MUNAKATA-EPC/Hercules_2022/KiCad_Project/2021/電源基板回路(2).pdf

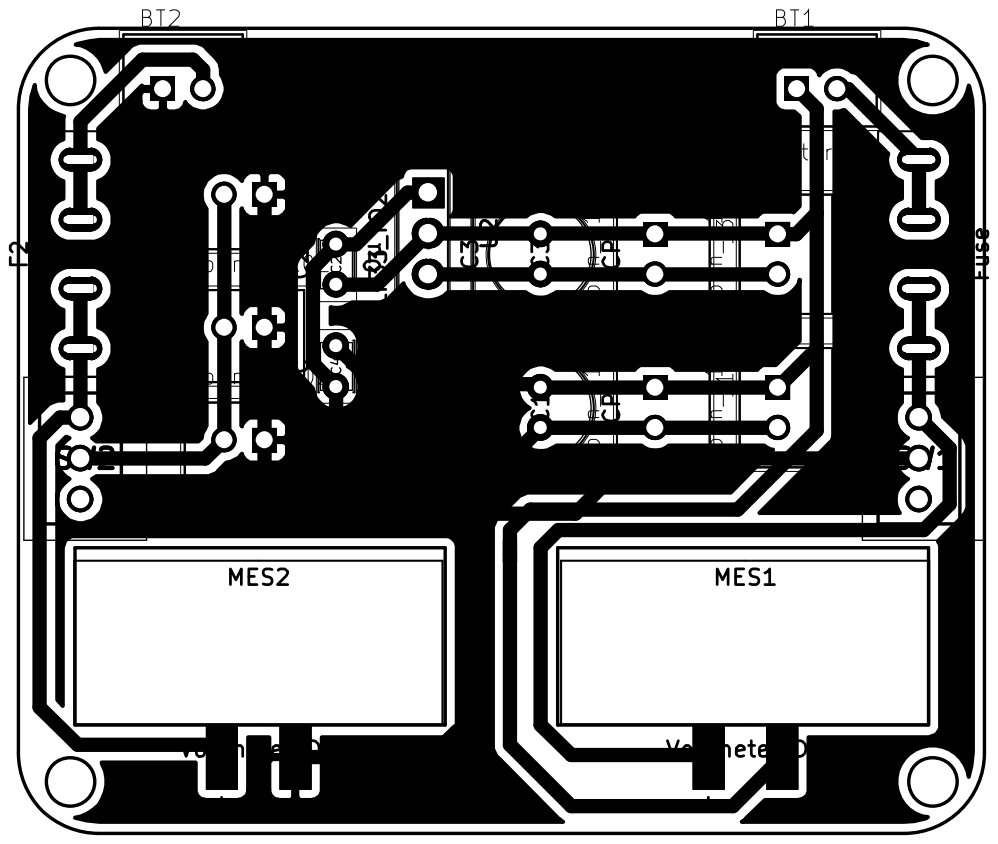
[picture p28: page 1]
