MUNAKATA-EPC/Hercules_2022/KEIHANNA_MAIN-teensy40/include/pid.h

void pid() {
  deviation = IMU_center - IMU;  //偏差:現在角度と目標角度のズレ

  val_I += deviation;  //偏差の積分値

  if (val_I < -30000) {
    val_I = -30000;
  } else if (val_I > 30000) {
    val_I = 30000;
  }

  if (abs(deviation) <= 2) {
    val_I = 0;
  }

  val_D = deviation - old_deviation;  //偏差の微分値
  old_deviation = deviation;  //微分用前回偏差値の保存

  operation_A = gain_P * deviation;  //比例ゲイン*偏差
  operation_B = gain_I * val_I;  //積分ゲイン*偏差の積分値
  operation_C = gain_D * val_D;  //微分ゲイン*偏差の微分値

  operation_A = operation_A + operation_B + operation_C;  //最終的な操作量

  if (operation_A < -set_limit_operation) {
    operation_A = -set_limit_operation;  //下限値
  } else if (operation_A > set_limit_operation) {
    operation_A = set_limit_operation; //上限値
  }
}
