MUNAKATA-EPC/Hercules_2022/KEIHANNA_MAIN-teensy40/include/control_LED.h

void control_LED() {
  if (digitalRead(LINE_1) == LOW || digitalRead(LINE_2) == LOW || digitalRead(LINE_3) == LOW || digitalRead(LINE_4) == LOW) {
    digitalWrite(LED, HIGH);
  } else {
    digitalWrite(LED, LOW);
  }
}
