MUNAKATA-EPC/Hercules_2022/OpenMV プログラム/FUKUDA ver 6.py

#Single Color RGB565 Blob Tracking Example
#  福田ロボットの調整用
# This example shows off single color RGB565 tracking using the OpenMV Cam.

import sensor, image, time, math#ライブラリーの読み込み
from pyb import UART, LED, Pin, Timer, DAC#ライブラリーの読み込み

red_led   = LED(1)                  #下２１行目までLEDのセットアップ
green_led = LED(2)
blue_led  = LED(3)
ir_led    = LED(4)

def led_control(x):
 if   (x&1)==0: red_led.off()
 elif (x&1)==1: red_led.on()
 if   (x&2)==0: green_led.off()
 elif (x&2)==2: green_led.on()
 if   (x&4)==0: blue_led.off()
 elif (x&4)==4: blue_led.on()
 if   (x&8)==0: ir_led.off()
 elif (x&8)==8: ir_led.on()

threshold_index = 0 # 0 for red, 1 for green, 2 for blue

# Color Tracking Thresholds (L Min, L Max, A Min, A Max, B Min, B Max)
# The below thresholds track in general red/green/blue things. You may wish to tune them...
thresholds1 = [(8, 100, 39, 82, -26, 71)]#メイン
#thresholds1 = [(0, 100, 53, 63, 31, 39)]
#thresholds1 = [(45, 90, 13, 84, -1, 64)]#検証１
#thresholds1 = [(53, 88, 48, 85, -22, 40)]#検証2
thresholds3 = [(0, 0, 40, 73, 26, 57)]#ゴール（青色）
thresholds2 = [(0, 100, 11, 31, -67, -45)]#ゴール（青色）
#thresholds2 = [(0, 100, -12, 17, 45, 72)]#ゴール（黄色）
#上で色の変更可　ただLAB色空間での探知である
# generic_blue_thresholds
uart = UART(3, 115200, timeout_char=1000)

sensor.reset()
sensor.set_pixformat(sensor.RGB565)#カラースケール
sensor.set_framesize(sensor.QVGA)#解像度
sensor.skip_frames(time = 400)#描写速度
sensor.set_contrast(1)#コントラスト
sensor.set_brightness(-2)#明るさ
sensor.set_saturation(1)#彩
sensor.set_auto_gain(False) # must be turned off for color tracking
sensor.set_auto_whitebal(False,(-5.82073, -5.019987, 0.5176831))# must be turned off for color tracking
clock = time.clock()

tim1 = Timer(4, freq=1000)
#tim2 = Timer(8, freq=1000)

dac = DAC(Pin("P6"),bits=12)

# Only blobs that with more pixels than "pixel_threshold" and more area than "area_threshold" are
# returned by "find_blobs" below. Change "pixels_threshold" and "area_threshold" if you change the
# camera resolution. "merge=True" merges all overlapping blobs in the image.

while(True):  #メインループ
 n=0#ボールカラーを取ったブロックの個数（for文の繰り返した回数）
 N=0#ゴールの色を取ったブロックの個数（for文の繰り返した回数）
 m=0
 cut_fro_and_bak=130#画面上での横線の定義
 cut_lef_and_rig=160#画面上での縦線の定義
 count=0#ブロックの個数（今話使っていない
 areapf=0
 iwashi=0#取得したブロックの密度の最大値を保存
 haraga=0#取得したブロックの面積の最大値を保存
 shinya=0
 #akiya=[0,0,0,0,0,0,0,0,0,0,0,0,0,0,0,0,0,0,0,0]
 areaA=[0,0,0,0,0,0,0,0,0,0,0,0,0,0,0,0,0,0,0,0]#取得したブロックの面積を配列にして1つの関数に保存
 areaB=[0,0,0,0,0,0,0,0,0,0,0,0,0,0,0,0,0,0,0,0]#取得したブロックの面積を配列にして1つの関数に保存
 areaC=[0,0,0,0,0,0,0,0,0,0,0,0,0,0,0,0,0,0,0,0]
 rectA=[0,0,0,0,0,0,0,0,0,0,0,0,0,0,0,0,0,0,0,0]#取得したブロック（ボール）の中心のX座標、Y座標、ブロックの横幅、縦幅の値を配列にして1つの関数に保存
 rectB=[0,0,0,0,0,0,0,0,0,0,0,0,0,0,0,0,0,0,0,0]#取得したブロック（ゴール）の中心のX座標、Y座標、ブロックの横幅、縦幅の値を配列にして1つの関数に保存
 rectC=[0,0,0,0,0,0,0,0,0,0,0,0,0,0,0,0,0,0,0,0]
 cxA=[0,0,0,0,0,0,0,0,0,0,0,0,0,0,0,0,0,0,0,0]#取得したブロック（ボール）の中心のX座標のみを配列にして1つの関数に保存
 cxB=[0,0,0,0,0,0,0,0,0,0,0,0,0,0,0,0,0,0,0,0]#取得したブロック（ゴール）の中心のX座標のみを配列にして1つの関数に保存
 cxC=[0,0,0,0,0,0,0,0,0,0,0,0,0,0,0,0,0,0,0,0]
 cyA=[0,0,0,0,0,0,0,0,0,0,0,0,0,0,0,0,0,0,0,0]#取得したブロック（ボール）の中心のY座標のみを配列にして1つの関数に保存
 cyB=[0,0,0,0,0,0,0,0,0,0,0,0,0,0,0,0,0,0,0,0]#取得したブロック（ゴール）の中心のY座標のみを配列にして1つの関数に保存
 cyC=[0,0,0,0,0,0,0,0,0,0,0,0,0,0,0,0,0,0,0,0]
 val=[0,0,0,0,0,0,0,0,0,0,0,0,0,0,0,0,0,0,0,0]#画面中心のX座標
 vall=[0,0,0,0,0,0,0,0,0,0,0,0,0,0,0,0,0,0,0,0]#画面中心のY座標
 r=[0,0,0,0,0,0,0,0,0,0,0,0,0,0,0,0,0,0,0,0]#atan2を使って出した角度（単位ラジアン）
 rads=[0,0,0,0,0,0,0,0,0,0,0,0,0,0,0,0,0,0,0,0]#ｒによって出た角度を絶対値に
 riole=[0,0,0,0,0,0,0,0,0,0,0,0,0,0,0,0,0,0,0,0]#ボールの左右有無の判別用
 distanceA=[0,0,0,0,0,0,0,0,0,0,]
 distanceB=[0,0,0,0,0,0,0,0,0,0,]#付け加え三平方
 densityA=[0,0,0,0,0,0,0,0,0,0,0,0,0,0,0,0,0,0,0,0]#ボールの色の取った面積に対する密度
 densityB=[0,0,0,0,0,0,0,0,0,0,0,0,0,0,0,0,0,0,0,0]#ゴールの色の取った面積に対する密度
 clock.tick()
 img = sensor.snapshot()
 for blob in img.find_blobs([thresholds1[threshold_index]], pixels_threshold=1, area_threshold=1, merge=True,margin=25):#下９０行目までカラーボールトラッキング
     n+=1
     cxA[n]=blob.cy()
     cyA[n]=blob.cx()
     rectA[n]=blob.rect()
     val[n]=blob.cy()-cut_fro_and_bak#値の調整　画面中央を座標(0,0)に
     vall[n]=blob.cx()-cut_lef_and_rig
     r[n]=int(math.atan2(-vall[n],-val[n])*100*0.31)#範囲の調整片側１８０度
     #distanceA[n]=int((math.sqrt((math.pow(val[n],2))+(math.pow(vall[n],2))))*29.16666666666667)#２点間の距離の公式
     distanceA[n]=int((math.sqrt((math.pow(val[n],2))+(math.pow(vall[n],2)))))
     rads[n]=abs(r[n])#atan2で出した値を絶対値に修正
     densityA[n]=blob.density()
     areaA[n]=blob.area()
     count=blob.count()#使ってない
     #distanceB[n]=int(math.sqrt(vall[n]^2+val[n]^2))#付け加え三平方
     if vall[n]>0:
         riole[n]=100#light or left
     else:
         riole[n]=0

     #area.append(blob.area())
     for i in range(16):#見えたときの確認用LED
        led_control(2)
 for blob in img.find_blobs([thresholds2[threshold_index]], pixels_threshold=10, area_threshold=10, merge=True,margin=30):#ゴール認識用カラートラッキング
     #ブロック計測用の変数はnからNへ変更
     #現状ゴールはエリアのサイズで測定しているが今後密度比への変更を予定
     N+=1
     cxB[N]=blob.cx()
     cyB[N]=blob.cy()
     rectB[N]=blob.rect()
     densityB[N]=blob.density()
     areaB[N]=blob.area()
 for blob in img.find_blobs([thresholds3[threshold_index]], pixels_threshold=10, area_threshold=10, merge=True,margin=30):#ゴール認識用カラートラッキング
     m+=1
     cxC[m]=blob.cx()
     cyC[m]=blob.cy()
     rectC[m]=blob.rect()
     #densityC[m]=blob.density()
     areaC[m]=blob.area()
     #akiya[m]=int(cyC[m]*17.0625)
 for i in range(16):#見えないときはオフ
      led_control(0)
 iwashi=(max(areaA[:]))
 haraga=(max(areaB[:]))
 shinya=(max(areaC[:]))


 if areaA[1]==iwashi!=0:#ボールの色を整理　補足したブロックの密度で判別しソート
     img.draw_rectangle(rectA[1])#長方形の生成
     img.draw_cross(cyA[1], cxA[1]) #中央のバツの生成
     ch1 = tim1.channel(1, Timer.PWM, pin=Pin("P7"), pulse_width_percent=rads[1])
     ch2 = tim1.channel(2, Timer.PWM, pin=Pin("P8"), pulse_width_percent=riole[1])
     ch3 = tim1.channel(3, Timer.PWM, pin=Pin("P9"), pulse_width_percent=distanceA[1])
     dac.write(distanceA[1])
 elif areaA[2]==iwashi!=0:
     img.draw_rectangle(rectA[2])#長方形の生成ynq4wtbeh fgnh
     img.draw_cross(cyA[2], cxA[2]) #中央のバツの生成
     ch1 = tim1.channel(1, Timer.PWM, pin=Pin("P7"), pulse_width_percent=rads[2])
     ch2 = tim1.channel(2, Timer.PWM, pin=Pin("P8"), pulse_width_percent=riole[2])
     ch3 = tim1.channel(3, Timer.PWM, pin=Pin("P9"), pulse_width_percent=distanceA[2])
     dac.write(distanceA[2])
 elif areaA[3]==iwashi!=0:
     img.draw_rectangle(rectA[3])#長方形の生成
     img.draw_cross(cyA[3], cxA[3]) #中央のバツの生成
     ch1 = tim1.channel(1, Timer.PWM, pin=Pin("P7"), pulse_width_percent=rads[3])
     ch2 = tim1.channel(2, Timer.PWM, pin=Pin("P8"), pulse_width_percent=riole[3])
     ch3 = tim1.channel(3, Timer.PWM, pin=Pin("P9"), pulse_width_percent=distanceA[3])

     dac.write(distanceA[3])
 elif areaA[4]==iwashi!=0:
     img.draw_rectangle(rectA[4])#長方形の生成
     img.draw_cross(cyA[4], cxA[4]) #中央のバツの生成
     ch1 = tim1.channel(1, Timer.PWM, pin=Pin("P7"), pulse_width_percent=rads[4])
     ch2 = tim1.channel(2, Timer.PWM, pin=Pin("P8"), pulse_width_percent=riole[4])
     ch3 = tim1.channel(3, Timer.PWM, pin=Pin("P9"), pulse_width_percent=distanceA[4])
     dac.write(distanceA[4])
 elif areaA[5]==iwashi!=0:
     img.draw_rectangle(rectA[5])#長方形の生成
     img.draw_cross(cyA[5], cxA[5]) #中央のバツの生成
     ch1 = tim1.channel(1, Timer.PWM, pin=Pin("P7"), pulse_width_percent=rads[5])
     ch2 = tim1.channel(2, Timer.PWM, pin=Pin("P8"), pulse_width_percent=riole[5])
     ch3 = tim1.channel(3, Timer.PWM, pin=Pin("P9"), pulse_width_percent=distanceA[5])
     dac.write(distanceA[5])
 elif areaA[6]==iwashi!=0:
     img.draw_rectangle(rectA[6])#長方形の生成
     img.draw_cross(cyA[6], cxA[6]) #中央のバツの生成
     ch1 = tim1.channel(1, Timer.PWM, pin=Pin("P7"), pulse_width_percent=rads[6])
     ch2 = tim1.channel(2, Timer.PWM, pin=Pin("P8"), pulse_width_percent=riole[6])
     ch3 = tim1.channel(3, Timer.PWM, pin=Pin("P9"), pulse_width_percent=distanceA[6])
     dac.write(distanceA[6])
 elif areaA[7]==iwashi!=0:
     img.draw_rectangle(rectA[7])#長方形の生成
     img.draw_cross(cyA[7], cxA[7]) #中央のバツの生成
     ch1 = tim1.channel(1, Timer.PWM, pin=Pin("P7"), pulse_width_percent=rads[7])
     ch2 = tim1.channel(2, Timer.PWM, pin=Pin("P8"), pulse_width_percent=riole[7])
     ch3 = tim1.channel(3, Timer.PWM, pin=Pin("P9"), pulse_width_percent=distanceA[7])
 elif areaA[8]==iwashi!=0:
     img.draw_rectangle(rectA[8])#長方形の生成
     img.draw_cross(cyA[8], cxA[8]) #中央のバツの生成
     ch1 = tim1.channel(1, Timer.PWM, pin=Pin("P7"), pulse_width_percent=rads[8])
     ch2 = tim1.channel(2, Timer.PWM, pin=Pin("P8"), pulse_width_percent=riole[8])
     ch3 = tim1.channel(3, Timer.PWM, pin=Pin("P9"), pulse_width_percent=distanceA[8])
 elif areaA[9]==iwashi!=0:
     img.draw_rectangle(rectA[9])#長方形の生成
     img.draw_cross(cyA[9], cxA[9]) #中央のバツの生成
     ch1 = tim1.channel(1, Timer.PWM, pin=Pin("P7"), pulse_width_percent=rads[9])
     ch2 = tim1.channel(2, Timer.PWM, pin=Pin("P8"), pulse_width_percent=riole[9])
     ch3 = tim1.channel(3, Timer.PWM, pin=Pin("P9"), pulse_width_percent=distanceA[9])
 elif areaA[10]==iwashi!=0:
     img.draw_rectangle(rectA[10])#長方形の生成
     img.draw_cross(cyA[10], cxA[10]) #中央のバツの生成
     ch1 = tim1.channel(1, Timer.PWM, pin=Pin("P7"), pulse_width_percent=rads[10])
     ch2 = tim1.channel(2, Timer.PWM, pin=Pin("P8"), pulse_width_percent=riole[10])
     ch3 = tim1.channel(3, Timer.PWM, pin=Pin("P9"), pulse_width_percent=distanceA[10])
 elif areaA[11]==iwashi!=0:
     img.draw_rectangle(rectA[11])#長方形の生成
     img.draw_cross(cyA[11], cyA[11]) #中央のバツの生成
     ch1 = tim1.channel(1, Timer.PWM, pin=Pin("P7"), pulse_width_percent=rads[11])
     ch2 = tim1.channel(2, Timer.PWM, pin=Pin("P8"), pulse_width_percent=riole[11])
     ch3 = tim1.channel(3, Timer.PWM, pin=Pin("P9"), pulse_width_percent=distanceA[11])
 elif areaA[12]==iwashi!=0:
     img.draw_rectangle(rectA[12])#長方形の生成
     img.draw_cross(cyA[12], cyA[12]) #中央のバツの生成
     ch1 = tim1.channel(1, Timer.PWM, pin=Pin("P7"), pulse_width_percent=rads[12])
     ch2 = tim1.channel(2, Timer.PWM, pin=Pin("P8"), pulse_width_percent=riole[12])
     ch3 = tim1.channel(3, Timer.PWM, pin=Pin("P9"), pulse_width_percent=distanceA[12])
 elif areaA[13]==iwashi!=0:
     img.draw_rectangle(rectA[13])#長方形の生成
     img.draw_cross(cyA[13], cyA[13]) #中央のバツの生成
     ch1 = tim1.channel(1, Timer.PWM, pin=Pin("P7"), pulse_width_percent=rads[13])
     ch2 = tim1.channel(2, Timer.PWM, pin=Pin("P8"), pulse_width_percent=riole[13])
     ch3 = tim1.channel(3, Timer.PWM, pin=Pin("P9"), pulse_width_percent=distanceA[13])
 elif areaA[14]==iwashi!=0:
     img.draw_rectangle(rectA[14])#長方形の生成
     img.draw_cross(cyA[14], cyA[14]) #中央のバツの生成
     ch1 = tim1.channel(1, Timer.PWM, pin=Pin("P7"), pulse_width_percent=rads[14])
     ch2 = tim1.channel(2, Timer.PWM, pin=Pin("P8"), pulse_width_percent=riole[14])
     ch3 = tim1.channel(3, Timer.PWM, pin=Pin("P9"), pulse_width_percent=distanceA[14])
 elif areaA[15]==iwashi!=0:
     img.draw_rectangle(rectA[15])#長方形の生成
     img.draw_cross(cyA[15], cyA[15]) #中央のバツの生成
     ch1 = tim1.channel(1, Timer.PWM, pin=Pin("P7"), pulse_width_percent=rads[15])
     ch2 = tim1.channel(2, Timer.PWM, pin=Pin("P8"), pulse_width_percent=riole[15])
     ch3 = tim1.channel(3, Timer.PWM, pin=Pin("P9"), pulse_width_percent=distanceA[15])
 else:
     ch1 = tim1.channel(1, Timer.PWM, pin=Pin("P7"), pulse_width_percent=100)
     ch2 = tim1.channel(2, Timer.PWM, pin=Pin("P8"), pulse_width_percent=50)
     riole[1]=50 #つけくわえ


 img.draw_line(0,cut_fro_and_bak,320,cut_fro_and_bak)#横線
 img.draw_line(cut_lef_and_rig,0,cut_lef_and_rig,240)#縦線
 #dac.write(128)
 #print(iwashi,count,density[:])123 345
 #print(rads[1])
 #print(distanceA[1])
 #print("   ")
 #print(distanceB[1])
 #print(riole[1])
 print(sensor.get_rgb_gain_db())

 #uart.write("x")
 #uart.writechar(cxA[1])
 #uart.write("y")
 #uart.writechar(cyA[1])
 uart.write("x")
 uart.writechar(rads[1])
 uart.write("y")
 uart.writechar(distanceA[1])
 uart.write("z")
 uart.writechar(riole[1])
