MUNAKATA-EPC/Hercules_2022/OpenMV プログラム/fujita_ver_10_beta.py

import sensor, image, time, math#ライブラリーの読み込み
from pyb import UART, LED, Pin, Timer, DAC#ライブラリーの読み込み

red_led   = LED(1)                  #下２１行目までLEDのセットアップ
green_led = LED(2)
blue_led  = LED(3)
ir_led    = LED(4)

def led_control(x):
 if   (x&1)==0: red_led.off()
 elif (x&1)==1: red_led.on()
 if   (x&2)==0: green_led.off()
 elif (x&2)==2: green_led.on()
 if   (x&4)==0: blue_led.off()
 elif (x&4)==4: blue_led.on()
 if   (x&8)==0: ir_led.off()
 elif (x&8)==8: ir_led.on()

threshold_index = 0 #このプログラム上では0で固定(触るな)

# Color Tracking Thresholds (L Min, L Max, A Min, A Max, B Min, B Max)
thresholds1 = [(22, 100, 54, 96, -50, 77)]#メイン
thresholds2 = [(0, 100, -12, 17, 45, 72)]#ゴール（黄色）
thresholds3 = [(0, 0, 42, 73, 26, 57)]#ゴール（青色）
thresholds4 = [(44, 60, -16, 22, -28, -9)]#フィールド(緑色)

#上で色の変更可　ただLAB色空間での探知である
uart = UART(3, 115200, timeout_char = 100)
uart.init(115200, bits=8, parity=None, stop=1, timeout_char=1000)
#uart1 = UART(1, 115200, timeout_char=1000)

sensor.reset()
sensor.set_pixformat(sensor.RGB565)#カラースケール
sensor.set_framesize(sensor.QVGA)#解像度
sensor.skip_frames(time = 400)#描写速度
sensor.set_contrast(1)#コントラスト
sensor.set_brightness(-3)#明るさ
sensor.set_saturation(0)#彩度
sensor.set_auto_gain(False) # must be turned off for color tracking
sensor.set_auto_whitebal(False,(-5.02073, -5.019987, 0.6176831))# must be turned off for color tracking
clock = time.clock()

tim1 = Timer(4, freq=1000)
#tim2 = Timer(8, freq=1000)

# Only blobs that with more pixels than "pixel_threshold" and more area than "area_threshold" are
# returned by "find_blobs" below. Change "pixels_threshold" and "area_threshold" if you change the
# camera resolution. "merge=True" merges all overlapping blobs in the image.

while(True):  #メインループ
 n=0#ボールカラーを取ったブロックの個数（for文の繰り返した回数）
 N=0#ゴール(黄色)の色を取ったブロックの個数（for文の繰り返した回数）
 m=0#ゴール(青色)の色を取ったブロックの個数(for文の繰り返した回数)
 M=0#フィールドの色を取ったブロックの個数(for文の繰り返した回数)
 cut_fro_and_bak=107#画面上での横線の定義
 cut_lef_and_rig=162#画面上での縦線の定義
 iwashi=0#取得したブロックの密度の最大値を保存
 haraga=0
 shinya=0
 hogehoge=0#取得したブロック(フィールド)の密度の最大値を保存
 ball_number=0
 yellow_number=0
 blue_number=0
 field_number=0
 areaA=[0,0,0,0,0,0,0,0,0,0,0,0,0,0,0,0,0,0,0,0]#取得したブロックの面積を配列にして1つの関数に保存
 areaB=[0,0,0,0,0,0,0,0,0,0,0,0,0,0,0,0,0,0,0,0]#取得したブロックの面積を配列にして1つの関数に保存
 areaC=[0,0,0,0,0,0,0,0,0,0,0,0,0,0,0,0,0,0,0,0]
 areaD=[0,0,0,0,0,0,0,0,0,0,0,0,0,0,0,0,0,0,0,0]#取得したブロックの面積を配列にして1つの関数に保存
 rectA=[0,0,0,0,0,0,0,0,0,0,0,0,0,0,0,0,0,0,0,0]#取得したブロック（ボール）の中心のX座標、Y座標、ブロックの横幅、縦幅の値を配列にして1つの関数に保存
 rectB=[0,0,0,0,0,0,0,0,0,0,0,0,0,0,0,0,0,0,0,0]#取得したブロック（ゴール）の中心のX座標、Y座標、ブロックの横幅、縦幅の値を配列にして1つの関数に保存
 rectC=[0,0,0,0,0,0,0,0,0,0,0,0,0,0,0,0,0,0,0,0]
 rectD=[0,0,0,0,0,0,0,0,0,0,0,0,0,0,0,0,0,0,0,0]#取得したブロック(フィールド)の中心のX座標、Y座標、ブロックの横幅、縦幅の値を配列にして保存
 cxA=[0,0,0,0,0,0,0,0,0,0,0,0,0,0,0,0,0,0,0,0]#取得したブロック（ボール）の中心のX座標のみを配列にして1つの関数に保存
 cxB=[0,0,0,0,0,0,0,0,0,0,0,0,0,0,0,0,0,0,0,0]#取得したブロック（ゴール）の中心のX座標のみを配列にして1つの関数に保存
 cxC=[0,0,0,0,0,0,0,0,0,0,0,0,0,0,0,0,0,0,0,0]
 cxD=[0,0,0,0,0,0,0,0,0,0,0,0,0,0,0,0,0,0,0,0]#取得したブロック(フィールド)の中心のX座標のみを配列にして保存
 cyA=[0,0,0,0,0,0,0,0,0,0,0,0,0,0,0,0,0,0,0,0]#取得したブロック（ボール）の中心のY座標のみを配列にして1つの関数に保存
 cyB=[0,0,0,0,0,0,0,0,0,0,0,0,0,0,0,0,0,0,0,0]#取得したブロック（ゴール）の中心のY座標のみを配列にして1つの関数に保存
 cyC=[0,0,0,0,0,0,0,0,0,0,0,0,0,0,0,0,0,0,0,0]
 cyD=[0,0,0,0,0,0,0,0,0,0,0,0,0,0,0,0,0,0,0,0]#取得したブロック(フィールド)の中心のY座標のみを配列にして保存
 valA=[0,0,0,0,0,0,0,0,0,0,0,0,0,0,0,0,0,0,0,0]#画面中心のX座標
 valB=[0,0,0,0,0,0,0,0,0,0,0,0,0,0,0,0,0,0,0,0]
 valC=[0,0,0,0,0,0,0,0,0,0,0,0,0,0,0,0,0,0,0,0]
 valD=[0,0,0,0,0,0,0,0,0,0,0,0,0,0,0,0,0,0,0,0]
 vallA=[0,0,0,0,0,0,0,0,0,0,0,0,0,0,0,0,0,0,0,0]#画面中心のY座標
 vallB=[0,0,0,0,0,0,0,0,0,0,0,0,0,0,0,0,0,0,0,0]
 vallC=[0,0,0,0,0,0,0,0,0,0,0,0,0,0,0,0,0,0,0,0]
 vallD=[0,0,0,0,0,0,0,0,0,0,0,0,0,0,0,0,0,0,0,0]
 radsA=[0,0,0,0,0,0,0,0,0,0,0,0,0,0,0,0,0,0,0,0]#ｒによって出た角度を絶対値に
 radsB=[0,0,0,0,0,0,0,0,0,0,0,0,0,0,0,0,0,0,0,0]
 radsC=[0,0,0,0,0,0,0,0,0,0,0,0,0,0,0,0,0,0,0,0]
 radsD=[0,0,0,0,0,0,0,0,0,0,0,0,0,0,0,0,0,0,0,0]
 distanceA=[0,0,0,0,0,0,0,0,0,0,0,0,0,0,0,0,0,0,0,0]
 clock.tick()
 img = sensor.snapshot()
 for blob in img.find_blobs([thresholds1[threshold_index]], pixels_threshold=1, area_threshold=1, merge=True,margin=25):#下９０行目までカラーボールトラッキング
     n+=1
     cxA[n]=blob.cx()
     cyA[n]=blob.cy()
     rectA[n]=blob.rect()
     valA[n]=blob.cx()-cut_lef_and_rig#値の調整　画面中央を座標(0,0)に
     vallA[n]=blob.cy()-cut_fro_and_bak
     radsA[n]=int(((math.atan2(vallA[n],valA[n])*-57.32)+180)/2)#範囲の調整片側１８０度
     distanceA[n]=int((math.sqrt((math.pow(valA[n],2))+(math.pow(vallA[n],2)))))
     areaA[n]=blob.area()

     #area.append(blob.area())
     #for i in range(1):#見えたときの確認用LED
        #led_control(2)

 #for blob in img.find_blobs([thresholds2[threshold_index]], pixels_threshold=1, area_threshold=1, merge=True,margin=25):
     #N+=1
     #cxB[N]=blob.cx()
     #cyB[N]=blob.cy()
     #rectB[N]=blob.rect()
     #valB[N]=blob.cx()-cut_lef_and_rig#値の調整　画面中央を座標(0,0)に
     #vallB[N]=blob.cy()-cut_fro_and_bak
     #radsB[N]=int(((math.atan2(vallB[N],valB[N])*-57.32)+180)/2)#範囲の調整片側１８０度
     #areaB[N]=blob.area()

 #for blob in img.find_blobs([thresholds3[threshold_index]], pixels_threshold=1, area_threshold=1, merge=True,margin=25):
     #m+=1
     #cxC[m]=blob.cx()
     #cyC[m]=blob.cy()
     #rectC[m]=blob.rect()
     #valC[m]=blob.cx()-cut_lef_and_rig#値の調整　画面中央を座標(0,0)に
     #vallC[m]=blob.cy()-cut_fro_and_bak
     #radsC[m]=int(((math.atan2(vallC[m],valC[m])*-57.32)+180)/2)#範囲の調整片側１８０度
     #areaC[m]=blob.area()

 for blob in img.find_blobs([thresholds4[threshold_index]], pixels_threshold=1, area_threshold=1, merge=True,margin=25):
     M+=1
     cxD[M]=blob.cx()
     cyD[M]=blob.cy()
     rectD[M]=blob.rect()
     valD[M]=blob.cx()-cut_lef_and_rig#値の調整　画面中央を座標(0,0)に
     vallD[M]=blob.cy()-cut_fro_and_bak
     radsD[M]=int(((math.atan2(vallD[M],valD[M])*-57.32)+180)/2)#範囲の調整片側１８０度
     areaD[M]=blob.area()

 iwashi=(max(areaA[:]))
 haraga=(max(areaB[:]))
 shinya=(max(areaC[:]))
 hogehoge=(max(areaD[:]))

 if areaA[1]==iwashi!=0:#ボールの色を整理　補足したブロックの密度で判別しソート
     img.draw_rectangle(rectA[1])#長方形の生成
     img.draw_cross(cxA[1], cyA[1]) #中央のバツの生成
     ball_number=1
 elif areaA[2]==iwashi!=0:
     img.draw_rectangle(rectA[2])#長方形の生成
     img.draw_cross(cxA[2], cyA[2]) #中央のバツの生成
     ball_number=2
 elif areaA[3]==iwashi!=0:
     img.draw_rectangle(rectA[3])#長方形の生成
     img.draw_cross(cxA[3], cyA[3]) #中央のバツの生成
     ball_number=3
 elif areaA[4]==iwashi!=0:
     img.draw_rectangle(rectA[4])#長方形の生成
     img.draw_cross(cxA[4], cyA[4]) #中央のバツの生成
     ball_number=4
 elif areaA[5]==iwashi!=0:
     img.draw_rectangle(rectA[5])#長方形の生成
     img.draw_cross(cxA[5], cyA[5]) #中央のバツの生成
     ball_number=5
 elif areaA[6]==iwashi!=0:
     img.draw_rectangle(rectA[6])#長方形の生成
     img.draw_cross(cxA[6], cyA[6]) #中央のバツの生成
     ball_number=6
 elif areaA[7]==iwashi!=0:
     img.draw_rectangle(rectA[7])#長方形の生成
     img.draw_cross(cxA[7], cyA[7]) #中央のバツの生成
     ball_number=7
 elif areaA[8]==iwashi!=0:
     img.draw_rectangle(rectA[8])#長方形の生成
     img.draw_cross(cxA[8], cyA[8]) #中央のバツの生成
     ball_number=8
 elif areaA[9]==iwashi!=0:
     img.draw_rectangle(rectA[9])#長方形の生成
     img.draw_cross(cxA[9], cyA[9]) #中央のバツの生成
     ball_number=9
 elif areaA[10]==iwashi!=0:
     img.draw_rectangle(rectA[10])#長方形の生成
     img.draw_cross(cxA[10], cyA[10]) #中央のバツの生成
     ball_number=10
 elif areaA[11]==iwashi!=0:
     img.draw_rectangle(rectA[11])#長方形の生成
     img.draw_cross(cxA[11], cyA[11]) #中央のバツの生成
     ball_number=11
 elif areaA[12]==iwashi!=0:
     img.draw_rectangle(rectA[12])#長方形の生成
     img.draw_cross(cxA[12], cyA[12]) #中央のバツの生成
     ball_number=12
 elif areaA[13]==iwashi!=0:
     img.draw_rectangle(rectA[13])#長方形の生成
     img.draw_cross(cxA[13], cyA[13]) #中央のバツの生成
     ball_number=13
 elif areaA[14]==iwashi!=0:
     img.draw_rectangle(rectA[14])#長方形の生成
     img.draw_cross(cxA[14], cyA[14]) #中央のバツの生成
     ball_number=14
 elif areaA[15]==iwashi!=0:
     img.draw_rectangle(rectA[15])#長方形の生成
     img.draw_cross(cxA[15], cyA[15]) #中央のバツの生成
     ball_number=15
 else:
     ball_number=0

 if areaB[1]==haraga!=0:#ゴール(黄色)の色を整理　補足したブロックの密度で判別しソート
     img.draw_rectangle(rectB[1])#長方形の生成
     img.draw_cross(cxB[1], cyB[1]) #中央のバツの生成
     yellow_number=1
 elif areaB[2]==haraga!=0:
     img.draw_rectangle(rectB[2])#長方形の生成
     img.draw_cross(cxB[2], cyB[2]) #中央のバツの生成
     yellow_number=2
 elif areaB[3]==haraga!=0:
     img.draw_rectangle(rectB[3])#長方形の生成
     img.draw_cross(cxB[3], cyB[3]) #中央のバツの生成
     yellow_number=3
 elif areaB[4]==haraga!=0:
     img.draw_rectangle(rectB[4])#長方形の生成
     img.draw_cross(cxB[4], cyB[4]) #中央のバツの生成
     yellow_number=4
 elif areaB[5]==haraga!=0:
     img.draw_rectangle(rectB[5])#長方形の生成
     img.draw_cross(cxB[5], cyB[5]) #中央のバツの生成
     yellow_number=5
 elif areaB[6]==haraga!=0:
     img.draw_rectangle(rectB[6])#長方形の生成
     img.draw_cross(cxB[6], cyB[6]) #中央のバツの生成
     yellow_number=6
 elif areaB[7]==haraga!=0:
     img.draw_rectangle(rectB[7])#長方形の生成
     img.draw_cross(cxB[7], cyB[7]) #中央のバツの生成
     yellow_number=7
 elif areaB[8]==haraga!=0:
     img.draw_rectangle(rectB[8])#長方形の生成
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
 img.draw_line(cut_lef_and_rig,0,cut_lef_and_rig,240)#縦線

 uart.writechar(255)
 uart.writechar(radsA[ball_number])
 uart.writechar(distanceA[ball_number])
 #uart.writechar(radsB[yellow_number])
 #uart.writechar(radsC[blue_number])
 uart.writechar(radsD[field_number])
